nanikgeorge/FeaturingYouSAO/LTSpice/oscillator.asc

C2: cap; 10µ
C3: cap; 10µ
D1: LED
D2: LED
Q1: npn; 2N3904
Q2: npn; 2N3904
Q3: npn; 2N3904
Q4: npn; 2N3904
R1: res; 5.6k
R2: res; 150k
R3: res; 150k
R4: res; 5.6k
V1: battery; 2.8
Named nets: 0, VDD
.tran 5s
